undotcom/home-assistant-audio-speaker-v3/images/IMG_5273.jpg

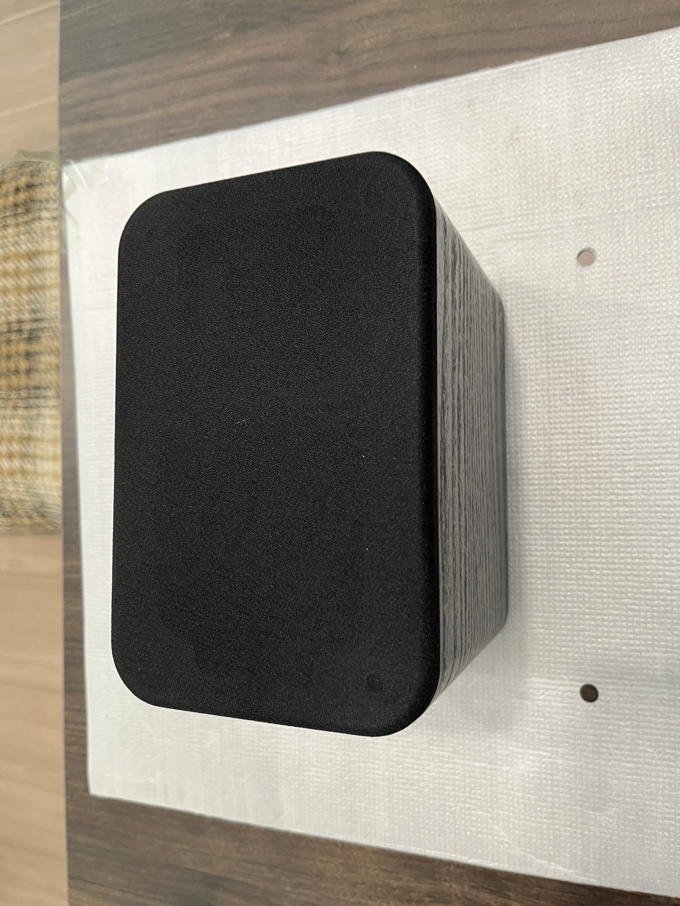
images/IMG_5273.jpg
