undotcom/home-assistant-audio-speaker-v3/images/IMG_5275.jpg

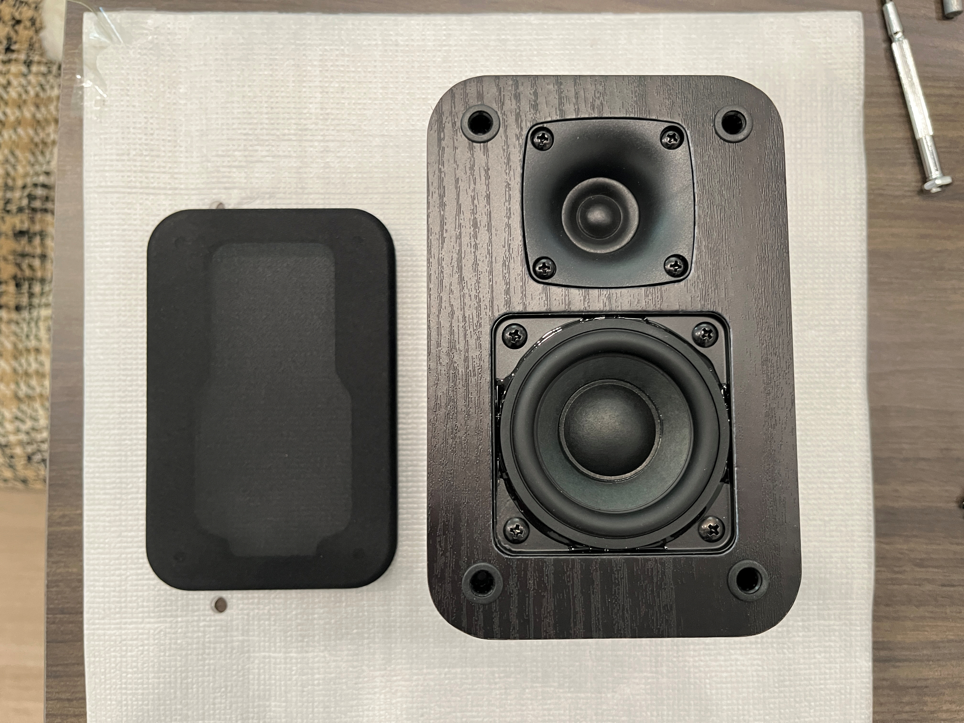
images/IMG_5275.jpg
